coolguyalex/GDMS-Pocket/data/Test/status.csv

hostile
sleeping
friendly
